afonsus1997/Hardware-MOD-Tracker-Player/Code/MODPlayer-32F4DISCO/Utilities/Media/Pictures/BMP_240x320/15.bmp

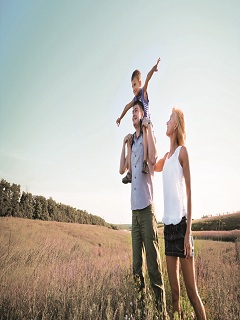
Code/MODPlayer-32F4DISCO/Utilities/Media/Pictures/BMP_240x320/15.bmp
