afonsus1997/Hardware-MOD-Tracker-Player/Code/MODPlayer-32F4DISCO/Utilities/Media/Pictures/BMP_240x240/24-bits/image03.bmp

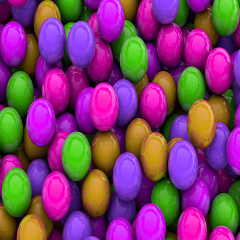
Code/MODPlayer-32F4DISCO/Utilities/Media/Pictures/BMP_240x240/24-bits/image03.bmp
