afonsus1997/Hardware-MOD-Tracker-Player/Code/MODPlayer-32F4DISCO/Utilities/Media/Pictures/Animated/BACK/image.bmp

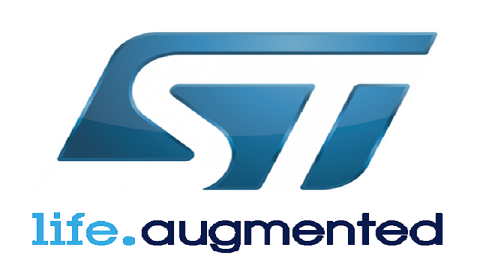
Code/MODPlayer-32F4DISCO/Utilities/Media/Pictures/Animated/BACK/image.bmp
