afonsus1997/Hardware-MOD-Tracker-Player/Code/MODPlayer-32F4DISCO/Utilities/Media/Pictures/BMP_128x160/1_16.bmp

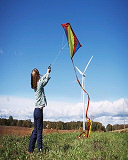
Code/MODPlayer-32F4DISCO/Utilities/Media/Pictures/BMP_128x160/1_16.bmp
