afonsus1997/Hardware-MOD-Tracker-Player/Code/MODPlayer-32F4DISCO/Utilities/Media/Pictures/BMP_240x240/16-bits/image04.bmp

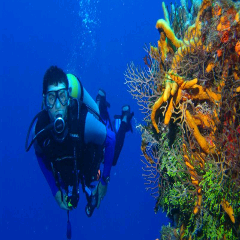
Code/MODPlayer-32F4DISCO/Utilities/Media/Pictures/BMP_240x240/16-bits/image04.bmp
