afonsus1997/Hardware-MOD-Tracker-Player/Code/MODPlayer-32F4DISCO/Utilities/Media/Pictures/JPG/Photo2.jpg

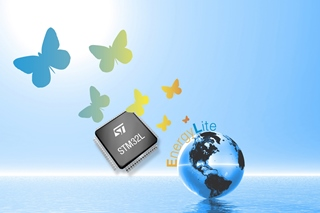
Code/MODPlayer-32F4DISCO/Utilities/Media/Pictures/JPG/Photo2.jpg
