afonsus1997/Hardware-MOD-Tracker-Player/Code/MODPlayer-32F4DISCO/Utilities/Media/Pictures/JPG/Photo5.jpg

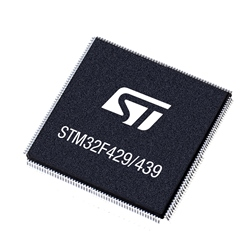
Code/MODPlayer-32F4DISCO/Utilities/Media/Pictures/JPG/Photo5.jpg
